brandon3055/emonMicro/hardware/1-port internal.jpg

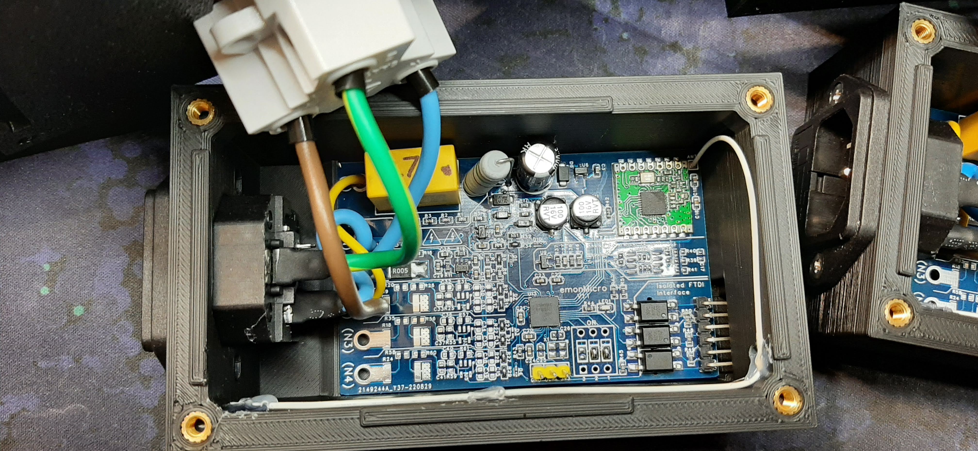
hardware/1-port internal.jpg
