brandon3055/emonMicro/hardware/Enclosure/cable adapter.jpg

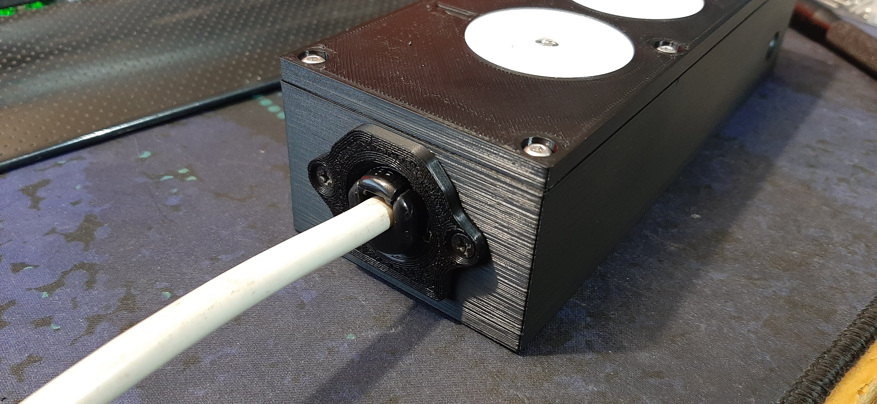
hardware/Enclosure/cable adapter.jpg
