brandon3055/emonMicro/hardware/Enclosure/FTDI Port Cover.stl

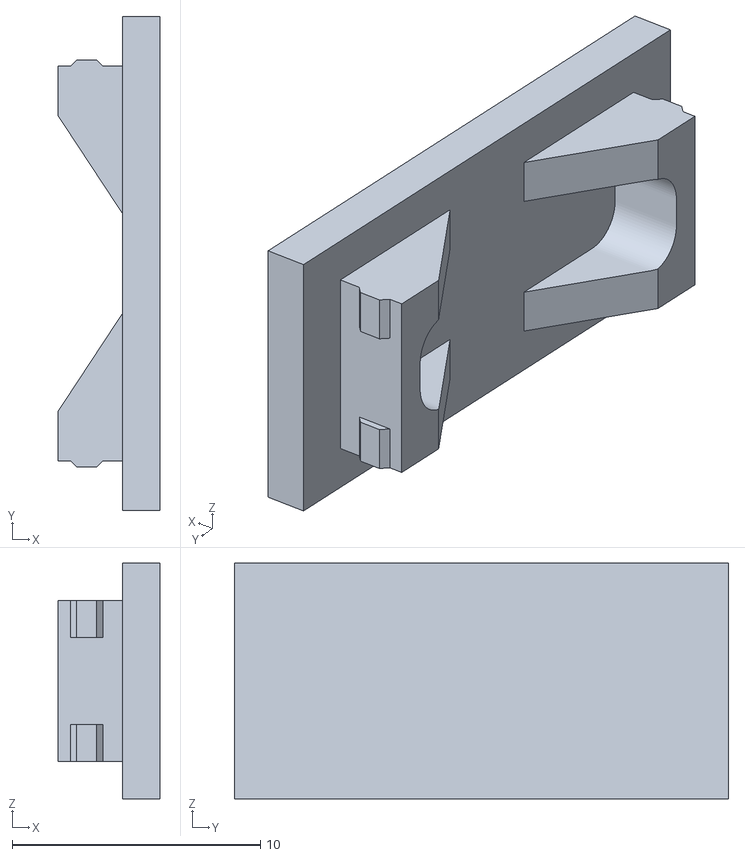
[picture p25: CAD file, 2022-10-14]
hardware/Enclosure/FTDI Port Cover.stl
4.10 x 19.9 x 9.50
