brandon3055/emonMicro/hardware/Enclosure/FTDI Port Cover - tight.stl

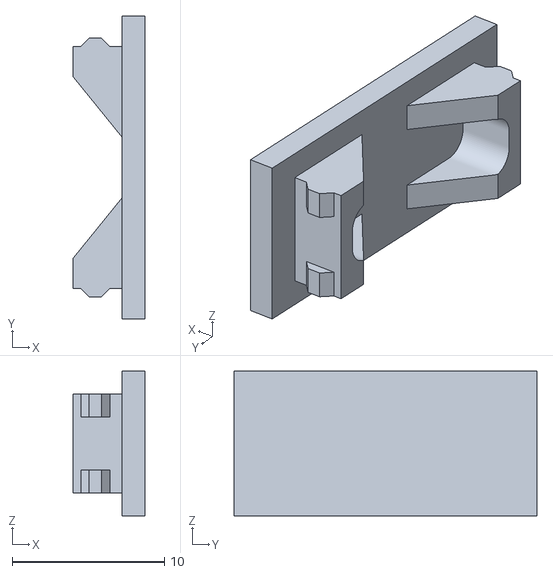
[picture p26: CAD file, 2022-10-14]
hardware/Enclosure/FTDI Port Cover - tight.stl
4.70 x 19.9 x 9.50
